StoneRose35/cortexguitarfx/Assets/fonts/Codepage737.png

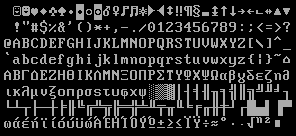
Assets/fonts/Codepage737.png
