StoneRose35/cortexguitarfx/Assets/fonts/sm_ascii_16x16.png

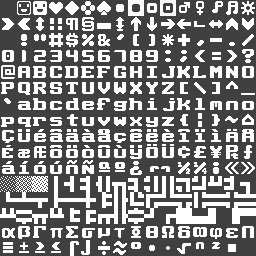
Assets/fonts/sm_ascii_16x16.png
