StoneRose35/cortexguitarfx/Inc/memFunctions.h

#ifndef _MEM_FUNCTIONS_H_
#define _MEM_FUNCTIONS_H_
#include "stdlib.h"

void * memcpy ( void * destination, const void * source, size_t num );

void * memset ( void * ptr, int value, size_t num );

#endif
