StoneRose35/cortexguitarfx/Src/common/consoleBase.c

#include <stdint.h>
#include "system.h"
#include "bufferedInputHandler.h"

extern uint8_t context; // used by printf to decide where a certain information should be output

extern CommBufferType usbCommBuffer __attribute__((aligned (256)));

extern CommBufferType btCommBuffer;

// TODO: properly handle the blocked case
// it seems data is sent multiple time when the output buffer would run over
void printf(const char* data)
{
	appendStringToOutputBuffer(&usbCommBuffer,data);
	/*
	uint32_t cnt = 0;
	uint8_t cur_data;
	uint8_t sc_res;
	cur_data = *(data + cnt);
	while (cur_data != 0)
	{
		if ((context & (1 << CONTEXT_USB)) == (1 << CONTEXT_USB))
		{
			 //while ( 
			//(*DMA_CH1_CTRL_TRIG & (1 << DMA_CH1_CTRL_TRIG_BUSY_LSB)) == (1 << DMA_CH1_CTRL_TRIG_BUSY_LSB)
			//);
			*(usbCommBuffer.outputBuffer+usbCommBuffer.outputBufferReadCnt) = *(data + cnt);
			usbCommBuffer.outputBufferReadCnt++;
			usbCommBuffer.outputBufferReadCnt &= ((1 << OUTPUT_BUFFER_SIZE)-1);

			if (usbCommBuffer.outputBufferReadCnt==((usbCommBuffer.outputBufferWriteCnt-1) & ((1 << OUTPUT_BUFFER_SIZE)-1))) // ring buffer full
			{
			    sc_res = sendCharAsyncUsb();
				while (sc_res == 0)
				{
					sc_res = sendCharAsyncUsb();
				}
				//while((*DMA_CH1_CTRL_TRIG & (1 << DMA_CH1_CTRL_TRIG_BUSY_LSB)) == (1 << DMA_CH1_CTRL_TRIG_BUSY_LSB));
			}
		}
		if ((context & (1 << CONTEXT_BT)) == (1 << CONTEXT_BT))
		{
			*(btCommBuffer.outputBuffer+btCommBuffer.outputBufferReadCnt) = *(data + cnt);
			btCommBuffer.outputBufferReadCnt++;
			btCommBuffer.outputBufferReadCnt &= ((1 << OUTPUT_BUFFER_SIZE)-1);

			if (btCommBuffer.outputBufferReadCnt==((1 << OUTPUT_BUFFER_SIZE)-1))
			{
				sc_res = sendCharAsyncBt();
				while (sc_res == 0)
				{
					sc_res = sendCharAsyncBt();
				}
			}
		}
		cnt++;
		cur_data = *(data + cnt);
	}
	//sendCharAsyncUsb();
	*/
}
