StoneRose35/cortexguitarfx/Src/rp2040/debugLed.c

#include "stdint.h"
#include "hardware/regs/addressmap.h"
#include "hardware/regs/sio.h"
#include "hardware/regs/io_bank0.h"
#include "hardware/rp2040_registers.h"
#include "drivers/debugLed.h"

void initDebugLed()
{
	*GPIO_OE &= ~(1 << RP2040_LED_PIN);
	*GPIO_OUT &= ~(1 << RP2040_LED_PIN);

    *DEBUG_LED_PIN_CNTR =  5; // function 5 (SIO)
	*GPIO_OE |= (1 << RP2040_LED_PIN);
}

void DebugLedOn()
{
    *(GPIO_OUT+1) = (1 << RP2040_LED_PIN);
}
void DebugLedOff()
{
    *(GPIO_OUT+2) = (1 << RP2040_LED_PIN);
}

void DebugLedToggle()
{
    *(GPIO_OUT+3) = (1 << RP2040_LED_PIN);
}
