StoneRose35/cortexguitarfx/Inc/drivers/core.h

/*
 * core.h
 *
 *  Created on: Oct 26, 2021
 *      Author: philipp
 */
#ifdef STM32
#ifndef CORE_H_
#define CORE_H_
#include <stdint.h>

#define CPACR ((volatile uint32_t*)0xE000ED88)

void enableFpu();

#endif /* CORE_H_ */
#endif
