StoneRose35/cortexguitarfx/Inc/intFunctions.h

/*
 * intFunctions.h
 *
 *  Created on: 11.10.2021
 *      Author: philipp
 */

#ifndef INC_INTFUNCTIONS_H_
#define INC_INTFUNCTIONS_H_

int compareUint8(const void*,const void*);

#endif /* INC_INTFUNCTIONS_H_ */
