StoneRose35/cortexguitarfx/Src/rp2040/pioStubs.c

#include "hardware/pio.h"

pio_sm_config pio_get_default_sm_config()
{
    pio_sm_config a;
    a.a = 0;
    return a;
}
void sm_config_set_wrap(pio_sm_config* c,uint32_t wt,uint32_t w)
 {

 }

void sm_config_set_sideset(pio_sm_config* c,int a,bool b,bool d)
 {

 }
